SuperPrintf/OpenCansPower/可乐充电宝V3.0/02-外壳模型（3D打印用）/可乐充电宝3.0-模型（18650x4-21700x4通用版）/18转21电池环.STL

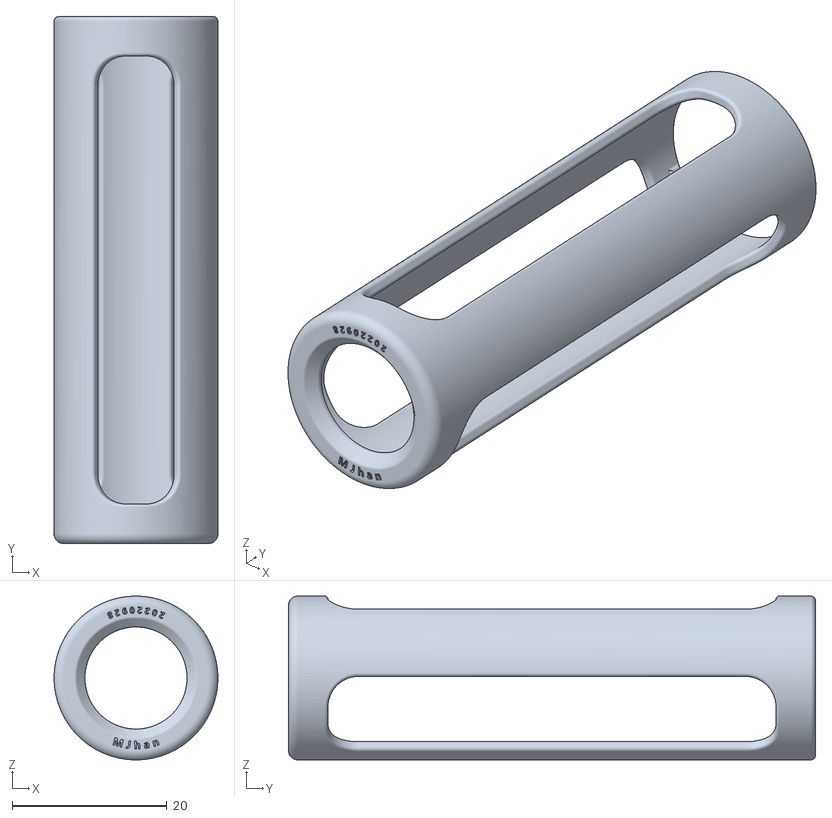
[picture p19: CAD file, 2022-09-28]
可乐充电宝V3.0/02-外壳模型（3D打印用）/可乐充电宝3.0-模型（18650x4-21700x4通用版）/18转21电池环.STL
21.2 x 68.2 x 21.2
